lu1198373615/MonikaSystem/photo/sch1V2.jpg

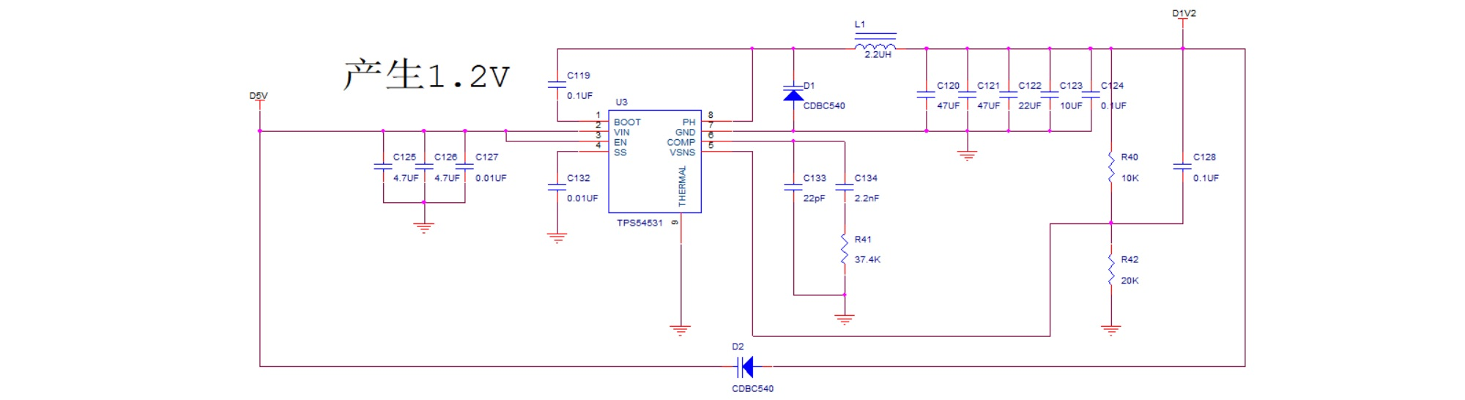
photo/sch1V2.jpg
